antibyte/NasMini.X/Video/cgrom.h

// Nascom 2 Font and extended graphics rom
// converted to the interleaved format needed by the video engine

static const unsigned char cgromx[]={
0x00, 0x7e, 0x7e, 0x6c, 0x10, 0x38, 0x10, 0x00, 0x00,
0x00, 0x00, 0x0f, 0x3c, 0x00, 0x7f, 0x99, 0x80, 0x02,
0x18, 0x66, 0x7f, 0x7e, 0x00, 0x18, 0x18, 0x18, 0x00,
0x00, 0x00, 0x00, 0x00, 0x00, 0x00, 0x30, 0x6c, 0x6c,
0x30, 0x00, 0x38, 0x60, 0x18, 0x60, 0x00, 0x00, 0x00,
0x00, 0x00, 0x06, 0x78, 0x30, 0x78, 0x78, 0x1c, 0xfc,
0x38, 0xfc, 0x78, 0x78, 0x00, 0x00, 0x18, 0x00, 0x60,
0x78, 0x7c, 0x30, 0xfc, 0x3c, 0xfc, 0xfe, 0xfe, 0x3c,
0xcc, 0x78, 0x1e, 0xe6, 0xf0, 0xc6, 0xc6, 0x38, 0xfc,
0x78, 0xfc, 0x78, 0xfc, 0xcc, 0xcc, 0xc6, 0xc6, 0xcc,
0xfe, 0x78, 0xc0, 0x78, 0x10, 0x00, 0x30, 0x00, 0xe0,
0x00, 0x1c, 0x00, 0x38, 0x00, 0xe0, 0x30, 0x18, 0xe0,
0x70, 0x00, 0x00, 0x00, 0x00, 0x00, 0x00, 0x00, 0x10,
0x00, 0x00, 0x00, 0x00, 0x00, 0x00, 0x1c, 0x18, 0xe0,
0x76, 0x10, 0x78, 0x00, 0x18, 0x7e, 0xcc, 0x60, 0x3c,
0x00, 0x7e, 0xcc, 0x60, 0xcc, 0x7c, 0x60, 0xcc, 0x30,
0x18, 0x00, 0x3e, 0x78, 0x00, 0x60, 0x78, 0x60, 0x00,
0xc6, 0xcc, 0x00, 0x38, 0x3a, 0x00, 0x0e, 0x18, 0x18,
0x0c, 0x0c, 0x76, 0x76, 0x3c, 0x3c, 0x30, 0x3c, 0x00,
0xe6, 0xe6, 0x00, 0x00, 0x00, 0x22, 0x55, 0xdd, 0x18,
0x18, 0x0c, 0x78, 0xc0, 0x3c, 0x36, 0x36, 0x00, 0x36,
0x18, 0xcc, 0x00, 0x18, 0x18, 0x00, 0x18, 0x00, 0x18,
0x76, 0x76, 0x36, 0x00, 0x36, 0x00, 0x36, 0x00, 0x36,
0x00, 0xd8, 0xfc, 0x78, 0xcc, 0x60, 0x00, 0x18, 0x78,
0xcc, 0x18, 0x00, 0xff, 0x00, 0x18, 0x60, 0xff, 0x18,
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
0x00, 0x08, 0x00, 0x08, 0x21, 0x21, 0x22, 0x21, 0x21,
0x22, 0x40, 0x40, 0x21, 0x41, 0x08, 0x04, 0x42, 0x40,
0x63, 0x61, 0x22, 0x41, 0x22, 0x41, 0x41, 0x08, 0x41,
0x41, 0x41, 0x41, 0x41, 0x01, 0x20, 0x40, 0x04, 0x08,
0x00, 0x18, 0x00, 0x40, 0x00, 0x02, 0x00, 0x12, 0x00,
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
};
