antibyte/NasMini.X/Z80/galax.h

static const byte galax[5901] ={
0x31, 0xf3, 0x28, 0xaf, 0x32, 0x25, 0x26, 0x3e,
0xa0, 0x32, 0x26, 0x26, 0x21, 0xad, 0x1c, 0xcd,
0x78, 0x14, 0x06, 0x05, 0x21, 0x00, 0x00, 0x2b,
0x7c, 0xb5, 0xc2, 0x17, 0x10, 0x05, 0xc2, 0x14,
0x10, 0xcd, 0x36, 0x15, 0x21, 0x39, 0x19, 0x11,
0xca, 0x0b, 0x01, 0x30, 0x00, 0xed, 0xb0, 0x11,
0x97, 0x08, 0xdd, 0x21, 0xad, 0x24, 0x0e, 0x0d,
0x0a, 0xc5, 0xdd, 0x6e, 0x00, 0xdd, 0x66, 0x01,
0xd5, 0xcd, 0x64, 0x15, 0x3e, 0x30, 0x12, 0x13,
0x13, 0x13, 0xdd, 0xe5, 0xe1, 0x23, 0x23, 0x01,
0x0e, 0x00, 0xed, 0xb0, 0x11, 0x10, 0x00, 0xdd,
0x19, 0xd1, 0xeb, 0x01, 0x40, 0x00, 0x09, 0xeb,
0xc1, 0x0d, 0xc2, 0x38, 0x10, 0xcd, 0x04, 0x14,
0x21, 0xad, 0x20, 0xcd, 0x78, 0x14, 0xcd, 0x04,
0x14, 0x21, 0x00, 0x00, 0x22, 0x16, 0x26, 0x22,
0x18, 0x26, 0x21, 0x2b, 0x26, 0x01, 0xc8, 0x01,
0x36, 0x00, 0x23, 0x0b, 0x78, 0xb1, 0xc2, 0x7f,
0x10, 0xcd, 0x36, 0x15, 0x3e, 0x32, 0x32, 0x23,
0x26, 0x3e, 0xff, 0x32, 0x24, 0x26, 0x3e, 0x01,
0x32, 0x27, 0x26, 0xdd, 0x21, 0x2b, 0x26, 0x06,
0x18, 0xaf, 0x32, 0x28, 0x26, 0xc5, 0x3a, 0x23,
0x26, 0xb7, 0xca, 0xce, 0x10, 0x3d, 0x32, 0x23,
0x26, 0xcc, 0xc8, 0x14, 0x3e, 0x96, 0xf5, 0x3e,
0x05, 0xf5, 0xf1, 0xf5, 0xf1, 0x3d, 0xc2, 0xb8,
0x10, 0xf1, 0x3d, 0xc2, 0xb5, 0x10, 0xcd, 0x8c,
0x15, 0xcd, 0xfb, 0x15, 0xcd, 0xce, 0x11, 0xdd,
0x7e, 0x00, 0xdd, 0xb6, 0x01, 0xc2, 0xde, 0x10,
0x06, 0x28, 0x10, 0xfe, 0xc3, 0xb7, 0x11, 0xcd,
0xce, 0x11, 0xcd, 0xe3, 0x13, 0xcd, 0x8c, 0x15,
0xcd, 0xfb, 0x15, 0xdd, 0x7e, 0x00, 0xdd, 0xb6,
0x01, 0xca, 0xb7, 0x11, 0x3a, 0x27, 0x26, 0xdd,
0x86, 0x00, 0xdd, 0x77, 0x00, 0xdd, 0x7e, 0x04,
0xdd, 0xb6, 0x05, 0xc2, 0xa1, 0x11, 0xcd, 0x73,
0x18, 0xdd, 0x7e, 0x00, 0xdd, 0x77, 0x02, 0xcd,
0x4d, 0x18, 0x3a, 0x24, 0x26, 0xb7, 0xc2, 0xa1,
0x11, 0x3a, 0x22, 0x26, 0xfe, 0x07, 0x3e, 0x10,
0xda, 0x25, 0x11, 0x3a, 0x26, 0x26, 0xcd, 0x4c,
0x14, 0xb7, 0xc2, 0xa1, 0x11, 0x3e, 0x05, 0xcd,
0x4c, 0x14, 0xd6, 0x02, 0xdd, 0x77, 0x04, 0xdd,
0x36, 0x05, 0x01, 0xdd, 0x7e, 0x06, 0xb7, 0xc2,
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
};
