antibyte/NasMini.X/Z80/nsys3.h

//NASYS 3 Monitor ROM
// 2K located ax 0x000
// Sourcecode attached below

static const byte nsysrom[2048] ={
0x31, 0x00, 0x10, 0xd7, 0x08, 0xc3, 0xfe, 0x03,
0xdf, 0x62, 0xd8, 0x18, 0xfb, 0xc3, 0xde, 0x03,
0xe3, 0x23, 0xe3, 0xe5, 0xf5, 0xc3, 0x84, 0x05,
0x18, 0xf6, 0xd7, 0x00, 0xdf, 0x66, 0xeb, 0xc9,
0xe3, 0x2b, 0xe3, 0xc3, 0x7d, 0x0c, 0x00, 0x00,
0xe3, 0x7e, 0x23, 0xb7, 0x20, 0x06, 0xe3, 0xc9,
0xe5, 0xc3, 0x55, 0x07, 0xf7, 0x18, 0xf2, 0x00,
0x3d, 0xc8, 0xf5, 0xf1, 0x18, 0xfa, 0xaf, 0x47,
0xff, 0xff, 0x10, 0xfc, 0xc9, 0xe5, 0x21, 0x00,
0x0c, 0xae, 0xd3, 0x00, 0x7e, 0xd3, 0x00, 0xe1,
0xc9, 0x3e, 0x10, 0xe5, 0x21, 0x00, 0x0c, 0xae,
0x77, 0x18, 0xf2, 0xf5, 0xd3, 0x01, 0xdb, 0x02,
0xcb, 0x77, 0x28, 0xfa, 0xf1, 0xc9, 0xc3, 0x7d,
0x0c, 0xe5, 0x2a, 0x32, 0x0c, 0xdf, 0x62, 0x38,
0x05, 0x2b, 0x7c, 0xb5, 0x20, 0xf7, 0xe1, 0xc9,
0x2a, 0x29, 0x0c, 0x56, 0x36, 0x5f, 0xd7, 0xe9,
0x72, 0xd8, 0xd7, 0xe5, 0x30, 0xf2, 0xc9, 0xdb,
0x02, 0x17, 0xd0, 0xdb, 0x01, 0xc9, 0xdf, 0x61,
0x30, 0x07, 0x2a, 0x2e, 0x0c, 0x22, 0x2c, 0x0c,
0xc9, 0x2a, 0x2c, 0x0c, 0x2b, 0x22, 0x2c, 0x0c,
0x7c, 0xb5, 0xc0, 0x21, 0x02, 0x0c, 0x01, 0x00,
0x08, 0x16, 0xff, 0x7d, 0xfe, 0x06, 0x20, 0x02,
0x16, 0xbf, 0xfe, 0x09, 0x20, 0x02, 0x16, 0xc7,
0x7e, 0xa2, 0x28, 0x06, 0x0e, 0x01, 0x7a, 0x2f,
0xa6, 0x77, 0x23, 0x10, 0xe4, 0x79, 0xb7, 0xc8,
0x2a, 0x30, 0x0c, 0x22, 0x2c, 0x0c, 0x3e, 0x02,
0xcd, 0x45, 0x00, 0x21, 0x01, 0x0c, 0xdb, 0x00,
0x2f, 0x77, 0x06, 0x08, 0x3e, 0x01, 0xcd, 0x45,
0x00, 0x23, 0xdb, 0x00, 0x2f, 0xe6, 0x7f, 0x57,
0xae, 0x20, 0x04, 0x10, 0xef, 0xb7, 0xc9, 0xaf,
0xff, 0xdb, 0x00, 0x2f, 0xe6, 0x7f, 0x5f, 0x7a,
0xae, 0x0e, 0xff, 0x16, 0x00, 0x37, 0xcb, 0x12,
0x0c, 0x1f, 0x30, 0xfa, 0x7a, 0xa3, 0x5f, 0x7e,
0xa2, 0xbb, 0x28, 0xdf, 0x7e, 0xaa, 0x77, 0x7b,
0xb7, 0x28, 0xd8, 0x3a, 0x01, 0x0c, 0xe6, 0x10,
0xb0, 0x87, 0x87, 0x87, 0xb1, 0xd7, 0x50, 0x28,
0x06, 0xe6, 0x7f, 0xd7, 0x4a, 0x20, 0xc6, 0x79,
0x21, 0x01, 0x0c, 0xfe, 0x41, 0x38, 0x16, 0xfe,
0x5b, 0x30, 0x12, 0xcb, 0x66, 0x28, 0x01, 0x3f,
0x3a, 0x27, 0x0c, 0xcb, 0x47, 0x79, 0x28, 0x01,
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
};

/*
        ; NAS-SYS 3 (R1)
	; WRITTEN BY RICHARD BEAL

	; characters
	org	0
bs	equ	08h
lf	equ	0ah
cs	equ	0ch
cr	equ	0dh
cul	equ	11h
cur	equ	12h
cuu	equ	13h
cud	equ	14h
csl	equ	15h
csr	equ	16h
ch	equ	17h
ccr	equ	18h
esc	equ	1bh
cu	equ	5fh

	; rom addresses
rom	equ	0
djmp	equ	0d000h
yjmp	equ	0b000h
bprc	equ	0fffah
bprw	equ	0fffdh

	; video ram
vram	equ	0800h
vl1	equ	vram+10
vl2	equ	vl1+64
vl15	equ	vram+038ah
vend	equ	vram+0400h

	; workspace ram
ram	equ	0c00h
usrsp	equ	1000h

	; workspace
	org	rom
	.phase	0c00h
initz	equ	$
	; copy of port 0
port0	defs	1
	; keyboard status map
kmap	defs	9
	; command char
argc	defs	1
	; no of args
argn	defs	1
	; up to 10 args
arg1	defs	2
arg2	defs	2
arg3	defs	2
arg4	defs	2
arg5	defs	2
arg69	defs	8
arg10	defs	2
	; no of chars in hex value
numn	defs	1
	; hex value entered
numv	defs	2
	; bpt address
brkadr	defs	2
	; bpt value
brkval	defs	1
	; conflg not 0 if e command
conflg	defs	1
	; k option
_kopt	defs	1
	; x option
_xopt	defs	1
	; cursor position
cursor	defs	2
	; last command
argx	defs	1
	; repeat counter
kcnt	defs	2
	; initial repeat delay
klong	defs	2
	; repeat speed
kshort	defs	2
	; blink speed
kblink	defs	2
	; monitor stack
monstk	defs	02dh
stack	equ	$
	; register save area
rbc	defs	2
rde	defs	2
rhl	defs	2
raf	defs	2
rpc	defs	2
	; user sp
rsp	defs	2
	; end of reg save area
rsae	equ	$
initr	equ	$
	; length of ktab
_ktabl	defs	2
	; address of end of ktab
_ktab	defs	2
	; address of stab
_stab	defs	2
	; output table
_out	defs	2
	; input table
_in	defs	2
	; user jumps
_uout	defs	3
_uin	defs	3
	; nmi jump
_nmi	defs	3

	; end of workspace
inite	equ	$

	.dephase
	org	rom
	; start of monitor
start:
	ld	sp,usrsp
	rst	rcal
	defb	stmon-$-1
	jp	mret

	; get input
rin:	rst	scal
	defb	zin
	ret	c
	jr	rin

	; initialize monitor
stmon:	jp	strtb

	; relative call
	; inc ret address
rcal:	ex	(sp),hl
	inc	hl
	ex	(sp),hl
	push	hl
	push	af
	jp	rcalb

	; subroutine call
scal:	jr	rcal

	; output hl de, add to sum
tx1:	rst	rcal
	defb	tx2-$-1
tx2:	rst	scal
	defb	ztbcd3
	ex	de,hl
	ret

	; bpt
	; decrement pc on stack
brkpt:	ex	(sp),hl
	dec	hl
	ex	(sp),hl
	jp	_nmi
	defb	0,0 ; fill

	; output a string
prs:	ex	(sp),hl
prs1:	ld	a,(hl)
	inc	hl
	; output unless 0
	or	a
	jr	nz,prs2
	ex	(sp),hl
dret:	ret

	; output a char
rout:	push	hl
	jp	aout

	; more of prs
prs2:	rst	rout
	jr	prs1
	defb	0 ; fill

	; delay
rdel:	dec	a
	ret	z
	push 	af
	pop	af
	jr	rdel

	; delay
tdel:	xor	a
	ld	b,a
tdel2:	rst	rdel
	rst	rdel
	djnz	tdel2
	ret

	; set,  reset bit in P0
fflp:	push	hl
	ld	hl,port0
	xor	(hl)
	out	(0),a
	ld	a,(hl)
ff2:	out	(0),a
	pop	hl
	ret


	; flip bit 4 in P0
mflp:	ld	a,10h
	push	hl
	ld	hl,port0
	xor	(hl)
	ld	(hl),a
	jr	ff2

	; serial output to P1
srlx:	push	af
	out	(1),a
	; wait until output
srl4:	in	a,(2)
	bit	6,a
	jr	z,srl4
	pop	af
	ret

	; nmi restart
rnmi:	jp	_nmi

	; get input
bin:	push	hl
	ld	hl,(kblink)
bin2:	rst	scal
	defb	zin
	jr	c,bin8
	dec	hl
	ld	a,h
	or	l
	jr	nz,bin2
bin8:	pop	hl
	ret

	; blink until input
blink:	ld	hl,(cursor)
	ld	d,(hl)
	ld	(hl),cu
	rst	rcal
	defb	bin-$-1
	ld	(hl),d
	ret	c
	rst	rcal
	defb	bin-$-1
	jr	nc,blink
	ret

	; check serial in
srlin:	in	a,(2)
	rla
	ret	nc
	in	a,(1)
	ret

	; repeat keyboard routine
rkbd:	rst	scal
	defb	zkbd
	jr	nc,rk2
	; key pressed
	ld	hl,(klong)
	ld	(kcnt),hl
	ret
	; key not pressed
rk2:	ld	hl,(kcnt)
	dec	hl
	ld	(kcnt),hl
	ld	a,h
	or	l
	ret	nz
	; test and clear table
	ld	hl,kmap+1
	ld	bc,0800h
	; set up mask in d
rk3:	ld	d,0ffh
	ld	a,l
	cp	6
	jr	nz,rk5
	ld	d,0bfh
rk5:	cp	9
	jr	nz,rk6
	ld	d,0c7h
	; test for key down
rk6:	ld	a,(hl)
	and	d
	jr	z,rk7
	ld	c,1
	; clear keys down
	ld	a,d
	cpl
	and	(hl)
	ld	(hl),a
	; next row
rk7:	inc	hl
	djnz	rk3
	ld	a,c
	or	a
	ret	z
	; repeat speed
	ld	hl,(kshort)
	ld	(kcnt),hl

	; keyboard routine
	; reset kbd counter
kbd:	ld	a,2
	call	fflp
	; store row 0 in map
	ld	hl,kmap
	in	a,(0)
	cpl
	ld	(hl),a

	; scan 8 rows
	ld	b,8
	; inc kbd counter
ksc1:	ld	a,1
	call	fflp
	inc	hl
	; get row status
	in	a,(0)
	cpl
	and	07fh
	ld	d,a
	; if map different
	;  find out why
	xor	(hl)
	jr	nz,ksc2
	; scan next row
ksc1a:	djnz	ksc1
	; no key pressed
ksc8:	or	a
	ret
	; wait to debounce
ksc2:	xor	a
	rst	rdel
	; get row again
	in	a,(0)
	cpl
	and	07fh
	ld	e,a
	; e = new state
	ld	a,d
	; a = old state
	xor	(hl)
	; a = changes
	; find changed bit
	ld	c,-1
	ld	d,0
	scf
ksc4:	rl	d
	inc	c
	rra
	jr	nc,ksc4
	; c = col changed
	; d= mask with 1 at change
	ld	a,d
	and	e
	ld	e,a
	; e= new state
	;  masked by change
	; if map state and new
	;  state equal, ignore
	ld	a,(hl)
	and	d
	cp	e
	jr	z,ksc1a
	; update map
	ld	a,(hl)
	xor	d
	ld	(hl),a
	; if new state is 0, then
	;  key released, so ignore
	ld	a,e
	or	a
	jr	z,ksc1a

	; value = srrrrccc
	;  s=1 if shift
	;  rrrr=9-row number
	;  ccc=column number
	ld	a,(kmap)
	and	10h
	or	b
	add	a,a
	add	a,a
	add	a,a
	or	c

	; search table
	rst	rcal
	defb	kse-$-1
	jr	z,ksc5
	; check for unshifted
	and	07fh
	rst	rcal
	defb	kse-$-1
	jr	nz,ksc8
	; set a to ascii value
ksc5:	ld	a,c

	; support lower case
	ld	hl,kmap
	cp	"A"
	jr	c,k20
	cp	"Z"+1
	jr	nc,k20
	; is it a letter
	bit	4,(hl)
	; 1= shift down
	jr	z,k7
	ccf
	; test option
k7:	ld	a,(_kopt)
	bit	0,a
	ld	a,c
	jr	z,k8
	ccf
k8:	jr	c,k20
	add	a,20h

	; control keys
	;  if not @, may modify
k20:	cp	"@"
	jr	nz,k30
	; if shift down, normal,
	;  otherwise ignore
	bit	4,(hl)
	jr	z,ksc8
	jr	k35
	; if @ down, modify
k30:	bit 5,(hl)
	jr	z,k35
	xor	40h
	; control
k35:	bit	3,(hl)
	jr	z,k40
	xor	40h
	; graphic
k40:	ld	hl,kmap+5
	bit	6,(hl)
	jr	z,k55
	xor	80h

	; k4 option
	;  change bit 7
k55:	ld	hl,_kopt
	bit	2,(hl)
	jr	z,k60
	xor	80h

	;  end
k60	scf
	ret

	; search keyboard table
kse:	ld	hl,(_ktab)
	ld	bc,(_ktabl)
	cpdr
	ret

	; workspace initialisation
	;  table
initt:	equ	$
	; length of ktab
iktabl:	defw	ktabe-ktab
	; end of keyboard table
iktab:	defw	ktabe-1
	; subroutine table
istab:	defw	staba-"A"-"A"
	; output table
iout:	defw	outt1
	; input table
iin:	defw	int1
	; user jumps
iuout:	jp	dret
iuin:	jp	dret
	; nmi jump
inmi:	defb	0c3h
initx:	equ	$

	; table with speeds
	; initial repeat delay
ilong:	defw	0280h
	; repeat delay
ishort	defw	0050h
	; blink speed
iblink	defw	0100h

	; crt routine
	;  ignore null or lf
crt:	or	a
	ret	z
	push	af
	cp	lf
	jr	z,crt2

	; clear screen
	cp	cs
	jr	nz,crt6
	; clear top line
	ld	hl,vl1
	push	hl
	ld	b,48
cr1:	ld	(hl)," "
	inc	hl
	djnz	cr1
	; set margin
	ld	b,16
cr3:	ld	(hl),0
	inc	hl
	djnz	cr3
	; copy down screen
	ex	de,hl
	pop	hl
	push	hl
	ld	bc,vend-vram-64-10-6
	ldir
	; set to top left
	pop	hl

	; set hl left side
crt0:	rst	scal
	defb	zcpos

	; save cursor
crt1:	ld	(cursor),hl

	; return
crt2:	pop	af
	ret

	; set hl to cursor
crt6:	ld	hl,(cursor)

	; bs, cul
	cp	bs
	jr	nz,crt14
crt8:	push	af
	; ignore margins
crt10:	dec hl
	ld	a,(hl)
	or	a
	jr	z,crt10
	pop	af
	cp	cul
	jr	z,crt12
	ld	(hl)," "
crt12:	rst	rcal
	defb	ctst-$-1
	jr	crt2
crt14:	cp	cul
	jr	z,crt8

	; cursor home, esc
	cp	ch
	jr	z,crt0
	cp	esc
	jr	nz,crt20
	rst	scal
	defb	zcpos
	ld	b,48
crt18:	ld	(hl)," "
	inc	hl
	djnz	crt18
	jr	crt0

	; new line, ccr
crt20:	cp	cr
	jr	z,crt38
	cp	ccr
	jr	nz,crt25
	push	hl
	rst	scal
	defb	zcpos
	pop	de
	or	a
	sbc	hl,de
	add	hl,de
	jr	z,crt1
	jr	crt38

	; cuu, cud
crt25:	cp	cuu
	jr	nz,crt28
	ld	de,-64
crt26:	add	hl,de
	rst	rcal
	defb	ctst-$-1
	jr	crt2
crt28:	cp	cud
	jr	nz,crt29
	ld	de,64
	jr	crt26

	; csl, csr
crt29:	cp	csl
	jr	nz,crt32
crt30:	inc	hl
	ld	a,(hl)
	dec	hl
	or	a
	jr	nz,crt31
	ld	(hl)," "
	jr	crt2
crt31:	ld	(hl),a
	inc	hl
	jr	crt30
crt32:	cp	csr
	jr	nz,crt34
	ld	b," "
crt33:	ld	a,(hl)
	or	a
	jr	z,crt2
	ld	(hl),b
	ld	b,a
	inc	hl
	jr	crt33

	; test foron screen
ctst:	ld	de,vl1
	or	a
	sbc	hl,de
	add	hl,de
	ret	c
	ld	de,vl15+48
	or	a
	sbc	hl,de
	add	hl,de
	ret	nc
	pop	af
ct8:	jp	crt1

	; cur, others
crt34:	cp	cur
	jr	z,crt36
	ld	(hl),a
	; ignore margins
crt36:	inc	hl
	ld	a,(hl)
	or	a
	jr	z,crt36

	; test need for cr
	ld	de,vl15+64
	or	a
	sbc	hl,de
	add	hl,de
	jr	nz,ct8

	; do new line
crt38:	rst	scal
	defb	zcpos
	ld	de,64
	add	hl,de
	rst	rcal
	defb	ctst-$-1

	; scroll up
crt40:	ld	de,vl1
	ld	hl,vl2
	ld	bc,vend-vram-64-64-16
	ldir
	; clear bottom line
	ld	b,48
crt50:	dec	hl
	ld	(hl)," "
	djnz	crt50
	jr	ct8

	; set hl to start of line
cpos:	ld	a,l
	and 	0c0h
	add	a,0ah
	ld	l,a
	ret

	; modify command
modify:	rst	scal
	defb	zargs
	; output address
mod1:	ld	(arg1),hl
	rst	scal
	defb	zsp2
	rst	scal
	defb	ztbcd3
	ld	a,(hl)
	rst	scal
	defb	zb2hex
	; get input line
	rst	prs
	defb	" ",cul,cul,cul,0
	rst	rcal
	defb	inls-$-1
	; get address
	rst	scal
	defb	znum
	jr	c,mod9
	ld	a,(hl)
	or	a
	jr	z,mod9
	inc	hl
	push	de
	ld	e,(hl)
	inc	hl
	ld	d,(hl)
	ex	de,hl
	pop	de
	ld	b,0
	; get each entry
mod2:	push	hl
	rst	scal
	defb	znum
	ld	a,(hl)
	or	a
	jr	z,mod3
	; put into memory
	inc	hl
	; hl = numn+1 = numv
	ld	a,(hl)
	pop	hl
mod2a:	ld	(hl),a
	inc	b
	inc	hl
	push	hl
mod3:	pop	hl
	ld	a,(de)
	; if "." return
	cp	"."
	ret	z
	; if "," set char
	cp	","
	jr	nz,mod4
	inc	de
	ld	a,(de)
	inc	de
	jr	mod2a
	; inc if none
mod4:	ld	a,b
	or	a
	jr	nz,mod5
	inc	hl
	; if ":" go back
mod5:	ld	a,(de)
	cp	":"
	jr	nz,mod7
	dec	hl
	dec	hl
	jr	mod1
	; if "/" set to value
mod7:	cp	"/"
	jr	nz,mod8
	inc	de
	rst	scal
	defb	znum
	jr	c,mod9
	ld	hl,(numv)
	jr	mod1
mod8:	or	a
	jr	z,mod1
	cp	" "
	jr	z,mod2
mod9:	rst	scal
	defb	zerrm
	jr	modify

	; routine to get input line
	; store bpt byte etc
inls:	rst	rcal
	defb	brst0-$-1
	; reset nmi address
	ld	hl,trap
	ld	(_nmi+1),hl
	; normal start of routine
	; get input char
inlin:	push	hl
inl2:	rst	scal
	defb	zblink
	rst	rout
	cp	a,cr
	jr	nz,inl2
	; set de to start of input
	ld	hl,(cursor)
	ld	de,-64
	add	hl,de
	ex	de,hl
	pop	hl
	ret

	; store bpt bytte abd
	;  set conflg to
brst0:	xor	a
	ld	(conflg),a
	ld	hl,(brkadr)
	ld	a,(hl)
	ld	(brkval),a
	ret

	; tabulate command
	; if hl>=de then end
tb1:	rst	scal
	defb	zcrlf
	pop	bc
	or	a
	sbc	hl,de
	add	hl,de
	ret	nc
	; control scrolling
tb2:	ld	a,b
	or	c
	jr	nz,tb3
	rst	rin
	cp	a,esc
	ret	z
	; start of routine
tabcde:	call	args3
tb3:	dec	bc
	push	bc
	; output address
	rst	scal
	defb	zsp2
	rst	scal
	defb	ztbcd3
	push	hl
	; output 8+arg4 bytes
	ld	a,(arg4)
	add	a,8
	ld	b,a
	push	bc
	; hex output
tb4:	ld	a,(arg5+1)
	or	a
	jr	nz,tb4a
	ld	a,(hl)
	rst	scal
	defb	zb2hex
	rst	scal
	defb	zspace
tb4a:	inc	hl
	djnz	tb4
	; ascii output
	rst	scal
	defb	zsp2
	pop	bc
	pop	hl
tb5:	ld	a,(arg5)
	or	a
	jr	nz,tb8
	ld	a,(hl)
	inc	a
	and	a,7fh
	cp	a,21h
	ld	a,(hl)
	jr	nc,tb6
	ld	a,"."
tb6:	rst	rout
tb8:	inc	hl
	djnz	tb5
	jr	tb1

	; output hl then space
tbcd3:	ld	a,h
	rst	scal
	defb	ztbcd2
	ld	a,l
	rst	scal
	defb	ztbcd2

	; output space
space:	ld	a," "
	rst	rout
	ret

	; output two spaces
sp2:	rst	rcal
	defb	space-$-1
	jr	space

	; error message
errm:	rst	prs
	defm	"Error"
	defb	0

	; output cr
crlf:	ld	a,cr
	rst	rout
	ret

	; add to checksum, output
tbcd2:	push	af
	add	a,c
	ld	c,a
	pop	af

	; output a
b2hex:	push	af
	rra
	rra
	rra
	rra
	rst	rcal
	defb	b1hex-$-1
	pop	af

	; output low half a
b1hex:	and	a,0fh
	add	a,90h
	daa
	adc	a,40h
	daa
	; output char
	rst	rout
	ret

	; read in hex value
	; de = input line
	; numn = no of chars
	; numv = value
num:	ld	a,(de)
	; ignore blanks
	cp	a," "
	inc	de
	jr	z,num
	dec	de
	; numv, numn = 0
	ld	hl,0
	ld	(numv),hl
	xor	a
	ld	hl,numn
	ld	(hl),a
	; get char
nn1:	ld	a,(de)
	; check for end
	or	a
	ret	z
	cp	a," "
	ret	z
	; convert from ascii
	; if lt 0 invalid
	sub	a,"0"
	ret	c
	; if lt 10 then ok, so nn2
	cp	10
	jr	c,nn2
	; convert a/f from ascii
	sub	a,"A"-"0"-10
	; if lt 10 invalid
	cp	a,10
	ret	c
	; if ge 16 invalid
	cp	a,16
	jr	c,nn2
	; invalid
	scf
	ret

	; valid char found
	; point to next char
nn2:	inc	de
	; inc numn
	inc	(hl)
	; put value in numv, rotating
	;  previous contents
	inc	hl
	rld
	inc	hl
	rld
	dec	hl
	dec	hl
	jr	z,nn1
	dec	de
	scf
	ret

	; get arguments
rlin:	ld	bc,argn
	xor	a
	ld	(bc),a
	; get value
	; cc set if invalid
rl2:	rst	scal
	defb	znum
	ret	c
	; check for end
	ld	a,(hl)
	or	a
	ret	z
	; copy to arg1/10
	inc	hl
	inc	bc
	ld	a,(hl)
	ld	(bc),a
	inc	hl
	inc	bc
	ld	a,(hl)
	ld	(bc),a
	; inc argn
	ld	hl,argn
	inc	(hl)
	ld	a,(hl)
	cp	a,11
	jr	c,rl2
	scf
	ret

	; monitor initialisation
	; restore bpt byte
strtb:	rst	rcal
	defb	brres-$-1
	; set workspace to 0
	ld	de,initz
	ld	b,initr-initz
	xor	a
st4:	ld	(de),a
	inc	de
	djnz	st4
	; set workspace from table
	ld	hl,initt
	ld	bc,inite-initr-2
	ldir
	; set speeds from table
	ld	de,klong
	ld	bc,6
	ldir
	; clear screen
	rst	prs
	defb	cs,0
	ret

	; user return
	;  reset stacks
mret:	ld	sp,stack
	ld	hl,usrsp
	ld	(rsp),hl
	rst	prs
	defm	"-- NAS-SYS 3 --"
	defb	cr,0
	rst	rcal
	defb	brres-$-1

	; main monitor loop
	;  get line and obey
parse:	call	inls
	ld	bc,argx
	; if command is blank, and
	;  previous commant not S,
	;  ignore it
	ld	a,(de)
	cp	a," "
	jr	nz,pa2
	ld	a,(bc)
	cp	"S"
	jr	nz,parse
	; check annd store
pa2:	cp	a,"A"
	jr	c,perr
	cp	"Z"+1
	jr	nc,perr
	ld	(bc),a
	ld	(argc),a
	; point to next char
	inc	de
	; get args
	rst	scal
	defb	zrlin
	jr	nc,pend
perr:	rst	scal
	defm	zerrm
	jr	parse
	; call command routine
pend:	rst	scal
	defb	zargs
	rst	scal
	defb	zscalj
pa7:	jr	parse

	; restore bpt byte
brres:	ld	hl,(brkadr)
	ld	a,h
	or	l
	ret	z
	ld	a,(brkval)
	ld	(hl),a
	ret

	; the execute command
	; conflg not 0 if e commanf
exec:	ld	a,-1
	ld	(conflg),a

	; execute and step commands
	; discard return
step:	pop	af
	; if no address entered,
	;   use stored user pc
	ld	a,(argn)
	or	a
	jr	z,exec2
	; user pc = new address
	ld	(rpc),hl
	; restore regs bc de hl af
exec2:	pop	bc
	pop	de
	pop	hl
	pop	af
	; restore user sp
	ld	sp,(rsp)
	; put user pc on top of stack
	push	hl
	ld	hl,(rpc)
	ex	(sp),hl
	; set bit 3 of p0, to
	;  activate nmi
	push	af
	ld	a,8
	out	(0),a
	pop	af
	; execute one step of program
	retn

	; come here after nmi or bpt
trap:	push	af
	push	hl
	; reset nmi bit in p0
	ld	a,(port0)
	out	(0),a
	; if conflg not 0 then e
	;  so execute normally
	ld	a,(conflg)
	or	a
	jr	z,er1
	; store bpt byte
	;  set conflg tp 0 for
	;   nmi or bpt,
	;   and insert restart
	call	brst0
	ld	a,h
	or	l
	jr	z,trap8
	ld	(hl),0e7h
	; execute program normally
trap8:	pop	hl
	pop	af
	retn

	; restore bpt byte,
	;  store user registers
er1:	rst	rcal
	defb	brres-$-1
	push	de
	push	bc
	; stack has: pc af hl de bc
	; set hl to user sp
	ld	hl,0
	add	hl,sp
	; set monitor sp
	ld	sp,stack
	; copy user regs from user
	;  stack to reg save area
	ld	de,stack
	ld	bc,10
	ldir
	; store user sp
	ld	(rsp),hl
	rst	rcal
	defb	pregs-$-1
	jr	pa7

	; output registers
pregs:	rst	prs
	defb	ccr,0
	; sp pc af hl de bc
	ld	hl,rsae
	ld	b,6
er2:	dec	hl
	ld	d,(hl)
	dec	hl
	ld	e,(hl)
	push	hl
	ex	de,hl
	ld	e,(hl)
	inc	hl
	ld	d,(hl)
	dec	hl
	rst	scal
	defb	ztx1
	pop	hl
	rst	scal
	defb	zsp2
	djnz	er2
	; i reg
	ld	a,i
	rst	scal
	defb	zb2hex
	rst	scal
	defb	zspace
	; ix iy regs
	push	ix
	pop	hl
	rst	scal
	defb	ztbcd3
	push	iy
	pop	hl
	rst	scal
	defb	ztbcd3
	; f reg
	ld	a,(raf)
	ld	de,estr-1
	ld	b,8
er4:	inc	de
	rla
	push	af
	ld	a,(de)
	jr	nc,er6
	rst	rout
er6:	pop	af
	djnz	er4
	rst	scal
	defb	zcrlf
	ret

	; string for flags
estr:	defb	"S","Z",0,"H"
	defb	0,"P","N","C"

	; get arguments
args:	ld	hl,(arg1)
args2:	ld	de,(arg2)
args3:	ld	bc,(arg3)
	ret

	; write command
write:	rst	scal
	defb	zmflp
	; wait
	rst	scal
	defb	ztdel
	; output to crt inly
	rst	scal
	defb	znnom
	push	hl
	; output 256 nulls
	xor a
	ld	b,a
w3:	rst	scal
	defb	zsrlx
	djnz	w3
	; calculate length-1
	rst	scal
	defb	zargs
w4:	rst	rcal
	defb	args2-$-1
	ex	de,hl
	scf
	sbc	hl,de
	; if len-1 is neg, end
	jp	c,r1y
	ex	de,hl
	; hl = start
	; de = length-1
	; wait
	xor	a
	rst	rdel
	; output 00 ff ff ff ff
	ld	b,5
w5:	rst	scal
	defb	zsrlx
	ld	a,0ffh
	djnz	w5
	; if block 0, set len to e+1
	xor	a
	cp	d
	jr	nz,w6
	ld	b,e
	inc	b
	; set e to length
w6:	ld	e,b
	; output start address
	ld	a,l
	rst	scal
	defb	zsrlx
	ld	a,h
	rst	scal
	defb	zsrlx
	; output length of data
	ld	a,e
	rst	scal
	defb	zsrlx
	; output block number
	ld	a,d
	rst	scal
	defb	zsrlx
	; now display all this
	; and output header checksum
	ld	c,0
	rst	scal
	defb	ztx1
	ld	a,c
	rst	scal
	defb	zsrlx
	; output the block
	rst	scal
	defb	zsout
	; output checksum and nulls
	ld	b,11
	ld	a,c
w9:	rst	scal
	defb	zsrlx
	xor	a
	djnz	w9
	; crlf (read has same timing)
	rst	scal
	defb	zcrlf
	jr	w4

	; icopy command
	; if arg1 ge arg2, goto
	;   ldir copy
icopy:	or	a
	sbc	hl,de
	add	hl,de
	jr	nc,copy
	; set to end not start
	dec	bc
	ex	de,hl
	add	hl,bc
	ex	de,hl
	add	hl,bc
	inc	bc
	lddr
	ret

	; copy command
copy:	ldir
	ret

	; atrithmetic command
arith:	ex	de,hl
	push	hl
	; sum
	add	hl,de
	rst	scal
	defb	ztbcd3
	; difference
	pop	hl
	or	a
	sbc	hl,de
	rst	scal
	defb	ztbcd3
	; offset
	dec	hl
	dec	hl
	ld	a,h
	rlc	l
	adc	a,0
	jr	z,aok
	; no good so ??
ang:	rst	prs
	defb	"?","?",cr,0
	ret
	; output offset
aok:	ld	a,l
	rrca
a7:	rst	scal
	defb	zb2hex
	jp	crlf

	; output comand
o:	ld	b,h
	ld	c,l
	out	(c),e
	ret

	; query command
q:	ld	b,h
	ld	c,l
	in	a,(c)
	jr	a7

	; relative call restart
rcalb:	push	de
	; set hl to ret adr
	ld	hl,6
	add	hl,sp
	ld	e,(hl)
	inc	hl
	ld	d,(hl)
	ex	de,hl
	dec	hl
	; rcal or scal
	dec	hl
	bit	3,(hl)
	inc	hl
	jr	nz,scal2
	; get offset
	ld	e,(hl)
	; e = offset, set d
	ld	a,e
	rla
	sbc	a,a
	ld	d,a
	inc	hl
	add	hl,de
rcal4:	pop	de
	pop	af
	ex	(sp),hl
	; fake jump to routine
	ret

	; subroutine call restart
	; get routine no.
scal2:	ld	e,(hl)
scal3:	ld	d,0
	ld	hl,(_stab)
	add	hl,de
	add	hl,de
	ld	e,(hl)
	inc	hl
	ld	d,(hl)
	ex	de,hl
	jr	rcal4

	; subroutine call
	;  routine no. at argc
scalj:	push	hl
	push	af
	push	de
	ld	hl,argc
	jr	scal2

	; souboutine for call
	;  routine no. in e
scali:	push	hl
	push	af
	push	de
	jr	scal3

	; keyboard table
ktab:	defb	0ffh,0ffh,0ffh,0ffh	; #00
	defb	0ffh,0ffh,0ffh,0ffh	; #04
	defb	008h,0ffh,08eh,0ffh	; #08 bs,lf
	defb	088h,009h,0ffh,0ffh	; #0c cs,cr
	defb	0ffh,03eh,02eh,046h	; #10 lru
	defb	036h,0beh,0aeh,00eh	; #14 dlr,ch
	defb	0ffh,0ffh,0ffh,089h	; #18 esc
	defb	0ffh,0ffh,0ffh,0ffh	; #1ch
	defb	014h,09ch,09bh,0a3h	; #20   "#
	defb	092h,0c2h,0bah,0b2h	; #24 $%&'
	defb	0aah,0a2h,098h,0a0h	; #28 ()*+
	defb	029h,00ah,021h,019h	; #2c ,-./
	defb	01ah,01ch,01bh,023h	; #30 0123
	defb	012h,042h,03ah,032h	; #34 4567
	defb	02ah,022h,018h,020h	; #38 89:;
	defb	0a9h,08ah,0a1h,099h	; #3c <=>?
	defb	00dh,02ch,041h,013h	; #40 @abc
	defb	03bh,033h,043h,010h	; #44 defg
	defb	040h,02dh,038h,030h	; #48 hijk
	defb	028h,031h,039h,025h	; #4c lmno
	defb	01dh,024h,015h,034h	; #50 pqrs
	defb	045h,035h,011h,02bh	; #54 tuvw
	defb	044h,03dh,03ch,01eh	; #58 xyz[
	defb	09eh,016h,09ah,096h	; #5c \]^_
ktabe	equ	$

	; keyboard command
	; store k options
kop:	ld	a,l
	ld	(_kopt),a
	ret

	; bpt command
	; store btp address
break:	ld	(brkadr),hl
	ret

	; generate command
	; output commands to both
g:	ld	hl,outt2
	rst	scal
	defb	znom
	push	hl
	ld	hl,gds
	ld	b,gdse-gds
g2:	ld	a,(hl)
	rst	rout
	; wait
	ld	c,20
	xor	a
g4:	rst	rdel
	dec	c
	jr	nz,g4
	inc	hl
	djnz	g2
	; output the data
	rst	scal
	defb	"W"
	; wait
	xor	a
	rst	rdel
	; output "E"
	ld	a,"E"
	rst	rout
	; output execution address
	ld	hl,(arg3)
	rst	scal
	defb	ztbcd3
	ld	a,cr
	; final cr, end
	rst	rout
	pop	hl
	rst	scal
	defb	znom
	ret

	; commands output by generate
gds:	defb	cr,"E","0",cr,"R",cr
gdse:	equ	$

	; string to serial output
	; hl = address
	; b = length
	; c = checksum
sout:	ld	c,0
so1:	ld	a,(hl)
	rst	scal
	defb	zsrlx
	add	a,c
	ld	c,a
	inc	hl
	djnz	so1
	ret

	; read routine
read:	rst	scal
	defb	zmflp
	; normal tables
	rst	scal
	defb	znnom
	push	hl
	rst	scal
	defb	znnim
	push	hl
	; look for 4 0ffh chars
	;  or 4 esc chars
r1:	ld	b,3
	ld	c,a
r2:	rst	rin
	cp	a,c
	jr	nz,r1
	djnz	r2
	cp	a,0ffh
	jr	z,r3
	cp	a,esc
	jr	nz,r1
	; end, restore tables
r1w:	rst	prs
	defb	ccr,0
r1x:	pop	hl
	rst	scal
	defb	znim
r1y:	pop	hl
	rst	scal
	defb	znom
	jp	mflp
	; get header data
r3:	rst	rin
	ld	l,a
	rst	rin
	ld	h,a
	rst	rin
	ld	e,a
	rst	rin
	ld	d,a
	; display and check
	ld	c,0
	rst	scal
	defb	ztx1
	rst	rin
	cp	a,c
	jr	nz,r6
	; offset
	ld	a,(argn)
	or	a
	jr	z,r3a
	ld	bc,(arg1)
	add	hl,bc
	; set b to length
r3a:	ld	b,e
	; load the data
	ld	c,0
r4:	ld	a,(argx)
	cp	a,"R"
	jr	z,r4a
	rst	rin
	jr	r4c
r4a:	rst	rin
	ld	(hl),a
r4c:	push	hl
	ld	hl,(cursor)
	ld	(hl),a
	pop	hl
	add	a,c
	ld	c,a
	inc	hl
	djnz	r4
	; check against checksum
	rst	rin
	cp	a,c
	jr	z,r7
	; error found
r6:	rst	prs
	defb	"?"," ",0
	jr	r1
	; cr, test for end
r7:	rst	prs
	defb	"."," ",0
	xor	a
	cp	a,d
	jr	nz,r1
	jr	r1w

	; use i/o command
up:	ld	hl,intu
	rst	scal
	defb	znim
	ld	hl,outtu
	rst	scal
	defb	znom
	ret

	; external (x) command
xp:	ld	a,l
	ld	(_xopt),a
	ld	hl,intx
	rst	scal
	defb	znim
	ld	hl,outtx
	rst	scal
	defb	znom
	ret

	; x input routine
	; check for input
xkbd:	rst	scal
	defb	zsrlin
	ret	nc
	; strip parity
	and	a,7fh
	; if full duplex, send back
	ld	hl,_xopt
	bit	5,(hl)
	call	z,xsopo
	; transparent mode
	bit	1,(hl)
	jr	nz,xk4
	; supply lf
	push	af
	rst	rcal
	defb	xsopl-$-1
	pop	af
	; if esccape or null entered
	;   assume program will no
	;   output the char
	or	a
	jr	z,xk4
	cp	a,esc
	jr	z,xk4
	set	7,(hl)
xk4:	scf
	ret

	; x output routine
xout:	push	af
	;  output unless bit 7 set
	;  to suppress serial output
	ld	hl,_xopt
	bit	7,(hl)
	call	z,xsop
	; turn on suppression
	res	7,(hl)
	pop	af
	ret

	; output char and lf
xsop:	rst	rcal
	defb	xsopo-$-1
	; if it was a cr and bit 4
	;  of $xopt = 0, output lf
xsopl:	cp	a,cr
	ret	nz
	bit	4,(hl)
	ret	nz
	ld	a,lf
	; output ascii char
	; set parity etc
xsopo:	or	a
	push	af
	; make parity even
	jp	pe,xsop2
	xor	a,80h
	; if bit 0 set, make it odd
xsop2:	bit	0,(hl)
	jr	z,xsop4
	xor	a,80h
	; output it
xsop4:	call	srlx
	; restore original value
	pop	af
	ret

	; terminal program
xn:	rst	scal
	defb	zinlin
	jr	xn

	; make $in and $out normal
normal:	rst	scal
	defb	znnim

	; set new output table
nnom:	ld	hl,outt1
nom:	push	hl
	ld	hl,(_out)
	ex	(sp),hl
	ld	(_out),hl
	pop	hl
	ret

	; set new input table
nnim:	ld	hl,int1
nim:	push	hl
	ld	hl,(_in)
	ex	(sp),hl
	ld	(_in),hl
	pop	hl
	ret

	; address table execution
in:	push	hl
	ld	hl,_in
	jr	ate
aout:	ld	hl,_out
	; get start of tbale
ate:	push	de
	push	bc
	ld	e,(hl)
	inc	hl
	ld	d,(hl)
	; get routine number
at4:	push	af
	ld	a,(de)
	inc	de
	; check for end
	or	a
	jr	z,at6
	ld	l,a
	pop	af
	; call routine
	push	de
	or	a
	ld	e,l
	call	scali
	pop	de
	jr	nc,at4
	push	af
at6:	pop	af
	pop	bc
	pop	de
	pop	hl
	ret

	; output tables
outt2:	defb	zcrt
	defb	zsrlx
	defb	0
outtx:	defb	zxout
outtu:	defb	zuout
outt1:	defb	zcrt
	defb	0

	; input tables
intu:	defb	zuin
int1:	defb	zrkbd
	defb	zsrlin
	defb	0
intx:	defb	zxkbd
	defb	zrkbd
	defb	0
	; subroutine table
	; starts with "A"
staba:	defw	arith
	defw	break
	defw	copy
	defw	djmp
	defw	exec
	defw	errm
	defw	g
	defw	xn
	defw	icopy
	defw	bprc
	defw	kop
	defw	errm
	defw	modify
	defw	normal
	defw	o
	defw	pregs
	defw	q
	defw	read
	defw	step
	defw	tabcde
	defw	up
	defw	read
	defw	write
	defw	xp
	defw	yjmp
	defw	bprw
	defw	mret	; 5bh
	defw	scalj	; 5ch
	defw	tdel	; 5dh
	defw	fflp	; 5eh
	defw	mflp	; 5fh
	defw	args	; 60h
	defw	kbd	; 61h
	defw	in	; 62h
	defw	inlin	; 63h
	defw	num	; 64h
	defw	crt	; 65h
	defw	tbcd3	; 66h
	defw	tbcd2	; 67h
	defw	b2hex	; 68h
	defw	space	; 69h
	defw	crlf	; 6ah
	defw	errm	; 6bh
	defw	tx1	; 6ch
	defw	sout	; 6dh
	defw	xout	; 6eh
	defw	srlx	; 6fh
	defw	srlin	; 70h
	defw	nom	; 71h
	defw	nim	; 72h
	defw	ate	; 73h
	defw	xkbd	; 74h
	defw	_uout	; 75h
	defw	_uin	; 76h
	defw	nnom	; 77h
	defw	nnim	; 78h
	defw	rlin	; 79h
	defw	b1hex	; 7ah
	defw	blink	; 7bh
	defw	cpos	; 7ch
	defw	rkbd	; 7dh
	defw	sp2	; 7eh
	defw	scali	; 7fh


	; subroutine call table
zmret	equ	5bh
zscalj	equ	5ch
ztdel	equ	5dh
zfflp	equ	5eh
zmflp	equ	5fh
zargs	equ	60h
zkbd	equ	61h
zin	equ	62h
zinlin	equ	63h
znum	equ	64h
zcrt	equ	65h
ztbcd3	equ	66h
ztbcd2	equ	67h
zb2hex	equ	68h
zspace	equ	69h
zcrlf	equ	6ah
zerrm	equ	6bh
ztx1	equ	6ch
zsout	equ	6dh
zxout	equ	6eh
zsrlx	equ	6fh
zsrlin	equ	70h
znom	equ	71h
znim	equ	72h
zate	equ	73h
zxkbd	equ	74h
zuout	equ	75h
zuin	equ	76h
znnom	equ	77h
znnim	equ	78h
zrlin	equ	79h
zb1hex	equ	7ah
zblink	equ	7bh
zcpos	equ	7ch
zrkbd	equ	7dh
zsp2	equ	7eh
zscali	equ	7fh

	; spare
	; --- none ---
nend	equ	$
	; end of listing
	end
	
 */
