antibyte/NasMini.X/Z80/rom.h

// Microsoft Z80 Basic

static const byte romdata[8192] ={
    0xf3, 0xc3, 0xb0, 0x00, 0xff, 0xff, 0xff, 0xff,
    0xc3, 0x9f, 0x00, 0xff, 0xff, 0xff, 0xff, 0xff,
    0xc3, 0x74, 0x00, 0xff, 0xff, 0xff, 0xff, 0xff,
    0xc3, 0xaa, 0x00, 0xff, 0xff, 0xff, 0xff, 0xff,
    0xff, 0xff, 0xff, 0xff, 0xff, 0xff, 0xff, 0xff,
    0xff, 0xff, 0xff, 0xff, 0xff, 0xff, 0xff, 0xff,
    0xff, 0xff, 0xff, 0xff, 0xff, 0xff, 0xff, 0xff,
    0x18, 0x00, 0xf5, 0xe5, 0xdb, 0x80, 0xe6, 0x01,
    0x28, 0x2d, 0xdb, 0x81, 0xf5, 0x3a, 0x44, 0x20,
    0xfe, 0x40, 0x20, 0x03, 0xf1, 0x18, 0x20, 0x2a,
    0x40, 0x20, 0x23, 0x7d, 0xfe, 0x40, 0x20, 0x03,
    0x21, 0x00, 0x20, 0x22, 0x40, 0x20, 0xf1, 0x77,
    0x3a, 0x44, 0x20, 0x3c, 0x32, 0x44, 0x20, 0xfe,
    0x20, 0x38, 0x04, 0x3e, 0xd6, 0xd3, 0x80, 0xe1,
    0xf1, 0xfb, 0xed, 0x4d, 0x3a, 0x44, 0x20, 0xfe,
    0x00, 0x28, 0xf9, 0xe5, 0x2a, 0x42, 0x20, 0x23,
    0x7d, 0xfe, 0x40, 0x20, 0x03, 0x21, 0x00, 0x20,
    0xf3, 0x22, 0x42, 0x20, 0x3a, 0x44, 0x20, 0x3d,
    0x32, 0x44, 0x20, 0xfe, 0x05, 0x30, 0x04, 0x3e,
    0x96, 0xd3, 0x80, 0x7e, 0xfb, 0xe1, 0xc9, 0xf5,
    0xdb, 0x80, 0xcb, 0x4f, 0x28, 0xfa, 0xf1, 0xd3,
    0x81, 0xc9, 0x3a, 0x44, 0x20, 0xfe, 0x00, 0xc9,
    0x21, 0x00, 0x20, 0x22, 0x40, 0x20, 0x22, 0x42,
    0x20, 0xaf, 0x32, 0x44, 0x20, 0x3e, 0x96, 0xd3,
    0x80, 0xed, 0x56, 0xfb, 0xc3, 0x00, 0x01, 0xff,
    0xff, 0xff, 0xff, 0xff, 0xff, 0xff, 0xff, 0xff,
    0xff, 0xff, 0xff, 0xff, 0xff, 0xff, 0xff, 0xff,
    0xff, 0xff, 0xff, 0xff, 0xff, 0xff, 0xff, 0xff,
    0xff, 0xff, 0xff, 0xff, 0xff, 0xff, 0xff, 0xff,
    0xff, 0xff, 0xff, 0xff, 0xff, 0xff, 0xff, 0xff,
    0xff, 0xff, 0xff, 0xff, 0xff, 0xff, 0xff, 0xff,
    0xff, 0xff, 0xff, 0xff, 0xff, 0xff, 0xff, 0xff,
    0xc3, 0x03, 0x01, 0xdd, 0x21, 0x00, 0x00, 0xc3,
    0x0e, 0x01, 0xc0, 0x09, 0x25, 0x11, 0x21, 0x45,
    0x20, 0xf9, 0xc3, 0x43, 0x1d, 0x11, 0xe1, 0x03,
    0x06, 0x63, 0x21, 0x45, 0x20, 0x1a, 0x77, 0x23,
    0x13, 0x05, 0xc2, 0x1d, 0x01, 0xf9, 0xcd, 0xe1,
    0x05, 0xcd, 0xb6, 0x0b, 0x32, 0xef, 0x20, 0x32,
    0x3e, 0x21, 0x21, 0xf6, 0x01, 0xcd, 0x43, 0x12,
    0xcd, 0xfe, 0x05, 0xcd, 0x0e, 0x09, 0xb7, 0xc2,
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
};
