antibyte/NasMini.X/Z80/zeap.h

// ZEAP 2.1 Assembler @ 0xd000

static const byte zeaprom[4115] ={
0xc3, 0x36, 0xdb, 0xc3, 0x78, 0xdb, 0x00, 0x20,
0x00, 0x50, 0xc3, 0xbf, 0xd3, 0x00, 0x00, 0x00,
0x00, 0x00, 0xff, 0xff, 0xff, 0xff, 0x00, 0x00,
0x00, 0x00, 0x00, 0x36, 0xd0, 0xaa, 0xd0, 0x8f,
0xd2, 0xf4, 0xd2, 0x91, 0x20, 0x2c, 0x98, 0x3b,
0x00, 0x82, 0x2b, 0x29, 0x27, 0xc0, 0x24, 0xa0,
0x23, 0x22, 0x80, 0x00, 0xa0, 0xa0, 0x56, 0x70,
0xd9, 0x55, 0x63, 0xd9, 0x4e, 0x13, 0xd9, 0x52,
0x78, 0xd9, 0x4f, 0x24, 0xd9, 0x41, 0x2d, 0xdd,
0x46, 0xa2, 0xd9, 0x58, 0x1e, 0xda, 0x5a, 0xfa,
0xd9, 0x49, 0x0b, 0xdb, 0x50, 0x5f, 0xd9, 0x3a,
0xcc, 0xdf, 0x48, 0x2c, 0xd9, 0x2b, 0x17, 0xd9,
0x2d, 0x1d, 0xd9, 0x57, 0x23, 0xdd, 0x4a, 0x51,
0xd9, 0x4b, 0x56, 0xd9, 0x47, 0x35, 0xd9, 0x59,
0xf3, 0xd8, 0x2f, 0x9d, 0xd9, 0x00, 0x5a, 0x45,
0x41, 0x50, 0x20, 0x32, 0x2e, 0x31, 0x2f, 0x41,
0x36, 0x34, 0x36, 0x20, 0x20, 0x46, 0x72, 0x65,
0x65, 0x3d, 0x20, 0x20, 0x20, 0x20, 0x20, 0x20,
0x45, 0x6e, 0x64, 0x3d, 0x20, 0x20, 0x20, 0x20,
0x20, 0x20, 0x45, 0x6e, 0x74, 0x3d, 0x5a, 0x5a,
0x5a, 0x5a, 0x5a, 0x5a, 0x5a, 0x20, 0xb9, 0x59,
0x75, 0x00, 0x80, 0x00, 0x01, 0x4c, 0x44, 0x60,
0x83, 0x78, 0x04, 0xf4, 0x3e, 0x04, 0xb1, 0x0d,
0x0a, 0x04, 0xe5, 0x1a, 0x04, 0xf3, 0x3a, 0x14,
0xec, 0x57, 0x14, 0xee, 0x5f, 0x03, 0x00, 0x83,
0x40, 0x04, 0xf4, 0x06, 0x03, 0x62, 0xf2, 0x21,
0x04, 0xf3, 0x2a, 0x03, 0x6a, 0xf2, 0x31, 0x04,
0xe2, 0xf9, 0x14, 0xf3, 0x7b, 0x03, 0x0c, 0xf2,
0x01, 0x14, 0xf3, 0x4b, 0x03, 0x73, 0xe2, 0x22,
0x14, 0x8c, 0x43, 0x04, 0xe0, 0x32, 0x03, 0x31,
0xe0, 0x02, 0x03, 0x65, 0xe0, 0x12, 0x13, 0xc9,
0xa0, 0x14, 0xd2, 0xb0, 0x13, 0xc4, 0xa8, 0x14,
0xd2, 0xb8, 0x13, 0x6c, 0xe0, 0x47, 0x13, 0x6e,
0xe0, 0x4f, 0x01, 0x4a, 0x52, 0xf8, 0x18, 0x03,
0x09, 0xf8, 0x20, 0x02, 0x50, 0xf2, 0xc3, 0x03,
0x06, 0xf2, 0xc2, 0x43, 0xe3, 0xe9, 0x01, 0x50,
0x55, 0x53, 0x48, 0x8f, 0xc5, 0x02, 0x4f, 0x50,
0x8f, 0xc1, 0x01, 0x43, 0x41, 0x4c, 0x4c, 0xf2,
0xcd, 0x05, 0x06, 0xf2, 0xc4, 0x02, 0x50, 0x83,
0xb8, 0x03, 0xf4, 0xfe, 0x03, 0xcc, 0x2f, 0x13,
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
