antibyte/NasMini.X/keymap.h

/* 
 * File:   keymap.h
 * Author: andi
 *
 * Created on 3. November 2013, 13:56
 */

#ifndef KEYMAP_H
#define	KEYMAP_H

// PS/2 scancode to Nascom keymatrix map
// the shift, alt(=GRA) and ctrl keys are not mapped
// but handled seperately

static const unsigned char keymap[9][8]={
    {0x00,0x00,0x00,0x00,0x00,0x00,0x00,0x00}, // scanline 0  -,-,-,-,-,-,-,-
    {0x33,0x32,0x2e,0x2b,0x22,0x2c,0x75,0x00}, // scanline 1  H,B,5,F,X,T,UP,-
    {0x3B,0x31,0x36,0x23,0x1a,0x35,0x6b,0x00}, // scanline 2  J,N,6,D,Z,Y,LEFT,-
    {0x42,0x3A,0x3d,0x24,0x1b,0x3c,0x72,0x00}, // scanline 3  K,M,7,E,S,U,DOWN,-
    {0x4b,0x41,0x3e,0x1d,0x1c,0x43,0x74,0x00}, // scanline 4  L,",",8,W,A,I,RIGHT,-
    {0x4c,0x49,0x46,0x26,0x15,0x44,0x00,0x00}, // scanline 5  ";",".",9,3,Q,O,GRA,-
    {0x52,0x4a,0x45,0x1e,0x16,0x4d,0x54,0x00}, // scanline 6  ":",/,0,2,1,P,[,-
    {0x34,0x2a,0x25,0x21,0x29,0x2d,0x5b,0x00}, // scanline 7  G,V,4,C,SPC,R,],-
    {0x66,0x5a,0x4e,0x00,0x00,0x0e,0x76,0x00}, // scanline 8  BS,ENT,"-",CTRL,SHIFT,@,HOME,-
};

// reduced PS/2 scancode map for filename input

static const unsigned char scancodes[40][2]={
    {0x1c,'A'}, {0x32,'B'}, {0x21,'C'}, {0x23,'D'},
    {0x24,'E'}, {0x2b,'F'}, {0x34,'G'}, {0x33,'H'},
    {0x43,'I'}, {0x3b,'J'}, {0x42,'K'}, {0x4b,'L'},
    {0x3a,'M'}, {0x31,'N'}, {0x44,'O'}, {0x4d,'P'},
    {0x15,'Q'}, {0x2d,'R'}, {0x1b,'S'}, {0x2c,'T'},
    {0x3c,'U'}, {0x2a,'V'}, {0x1d,'W'}, {0x22,'X'},
    {0x35,'Y'}, {0x1a,'Z'}, {0x45,'0'}, {0x16,'1'},
    {0x1e,'2'}, {0x26,'3'}, {0x25,'4'}, {0x2e,'5'},
    {0x36,'6'}, {0x3d,'7'}, {0x3e,'8'}, {0x46,'9'},
    {0x49,'.'}, {0x66,'-'}, {0x5a,'+'}, {0x76,'*'},       
};
    // - = Backspace, + = Enter, * = Escape

#endif	/* KEYMAP_H */
